sarfata/shirtty-addon/photo-2.jpeg

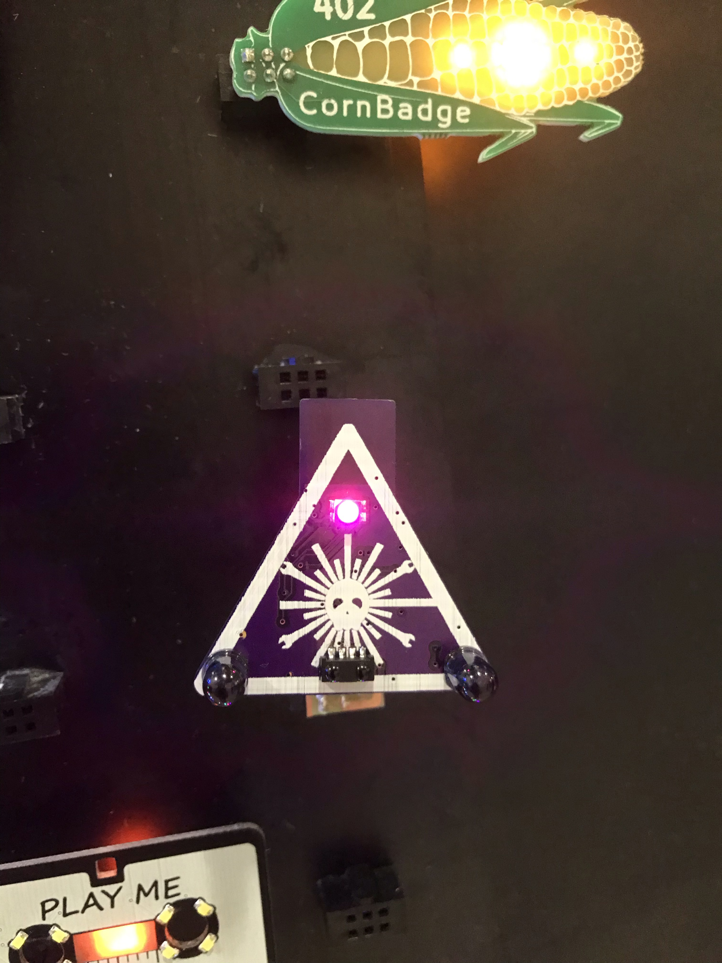
photo-2.jpeg
