sarfata/shirtty-addon/photo-3.jpeg

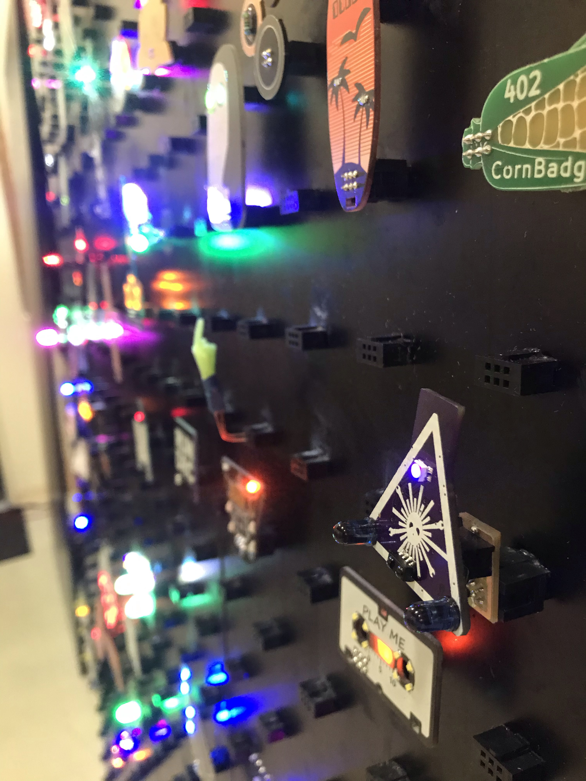
photo-3.jpeg
